cbwhickstein/Basic_Eurorack_Sequencer/Simulation/Draft1.asc

C1: cap; 10n
C2: cap; 10n
C3: cap; 10µ
D1: diode
D2: diode
D3: diode
D4: diode
D5: diode
D6: diode
D7: diode
D8: diode
D9: diode
D10: diode
D11: diode
D12: diode
Q1: npn
Q2: pnp
Q3: npn
Q4: pnp
Q5: npn
Q6: pnp
Q7: npn
Q8: pnp
Q9: npn
Q10: pnp
Q11: npn
Q12: pnp
Q13: npn
Q14: pnp
Q15: npn
Q16: pnp
Q17: npn
Q18: pnp
Q19: npn
Q20: pnp
Q21: npn
Q22: pnp
R1: res; 100k
R2: res; 100k
R3: res; 10k
R4: res; 10k
R5: res; 100k
R6: res; 1k
R7: res; 10k
R8: res; 10k
R9: res; 12k
R10: res; 1k
R11: res; 1k
R12: res; 1k
R13: res; 4.7k
R14: res; 4k7
R15: res; 10k
R16: res; 10k
R17: res; 12k
R18: res; 1k
R19: res; 4.7k
R20: res; 1k
R21: res; 10k
R22: res; 10k
R23: res; 12k
R24: res; 1k
R25: res; 4.7k
R26: res; 1k
R27: res; 10k
R28: res; 10k
R29: res; 12k
R30: res; 1k
R31: res; 4.7k
R32: res; 1k
R33: res; 10k
R34: res; 10k
R35: res; 12k
R36: res; 1k
R37: res; 4.7k
R38: res; 1k
R39: res; 10k
R40: res; 1k
R41: res; 12k
R42: res; 1k
R43: res; 4.7k
R44: res; 1k
R45: res; 10k
R46: res; 10k
R47: res; 12k
R48: res; 1k
R49: res; 4.7k
R50: res; 1k
R51: res; 10k
R52: res; 10k
R53: res; 12k
R54: res; 1k
R55: res; 4.7k
R56: res; 1k
R57: res; 10k
R58: res; 10k
R59: res; 12k
R60: res; 1k
R61: res; 4.7k
R62: res; 1k
R63: res; 10k
R64: res; 10k
R65: res; 12k
R66: res; 1k
R67: res; 4.7k
R68: res; 1k
R69: res; 10k
R70: res; 12k
R71: res; 1k
R72: res; 4.7k
R73: res; 10k
R74: res; 10k
R75: res; 10k
R76: res; 10k
R77: res; 10k
R78: res; 10k
R79: res; 10k
R80: res; 10k
R81: res; 10k
R82: res; 10k
R83: res; 10k
R84: res; 40k
R85: res; 10k
U1: OP07
U2: OP07
U3: OP07
U4: OP07
U5: OP07
U6: OP07
U7: OP07
U8: OP07
U9: OP07
U10: OP07
U11: OP07
U12: OP07
U13: OP07
U14: OP07
U15: OP07
V1: voltage; 24
V2: voltage; PULSE(0 12 0 0.01 0.01 0.1 0.2)
V3: voltage; PULSE(0 5 0.5 0.01m 0.01m 0.1 1)
V4: voltage; PULSE(0 5 0.6 0.01m 0.01m 0.1 1)
V5: voltage; PULSE(0 5 0.7 0.01m 0.01m 0.1 1)
V6: voltage; PULSE(0 5 0.8 0.01m 0.01m 0.1 1)
V7: voltage; PULSE(0 5 0 0.01m 0.01m 0.1 1)
V8: voltage; PULSE(0 5 0.1 0.01m 0.01m 0.1 1)
V9: voltage; PULSE(0 5 0.2 0.01m 0.01m 0.1 1)
V10: voltage; PULSE(0 5 0.3 0.01m 0.01m 0.1 1)
V11: voltage; PULSE(0 5 0.9 0.01m 0.01m 0.1 1)
V12: voltage; PULSE(0 5 0.4 0.01m 0.01m 0.1 1)
Named nets: +12, -12, 0, SQR, SQR_Buff, OUT, CLK, out0, out1, out2, out3, out4, out5, out6, out7, out8, out9
.tran 0 10 0 startup
f=tau/(R_5 x C_3)
---------------------------------------
---------------------------------------
---------------------------------------
---------------------------------------
---------------------------------------
---------------------------------------
---------------------------------------
R5 = poti
R8 Poti
CLK to CD4017BE
Output Stage for single output
R8 Poti
R8 Poti
R8 Poti
R8 Poti
R8 Poti
R8 Poti
R8 Poti
R8 Poti
R8 Poti
R8 Poti
